claasehmke/Remote-Controller-Accessory-for-Ventilators/Raspberry/include/tcp_messages.hpp

#ifndef REMOTE_CONTROLLER_RASPI_TCP_MESSAGES_HPP
#define REMOTE_CONTROLLER_RASPI_TCP_MESSAGES_HPP

namespace remote_controller_tcp {
// messages
    const uint32_t MSG_ACTUATOR_CONTROL_ID = 0x00;

    struct MSG_ACTUATOR_CONTROL{
        const int32_t message_id = MSG_ACTUATOR_CONTROL_ID;
        int32_t time;
        int32_t rotation_update; //bool
        int32_t rotation; //steps in both directions
        int32_t push_update; //bool
        int32_t push; //bool
    } __attribute__((packed));

}
#endif //REMOTE_CONTROLLER_RASPI_TCP_MESSAGES_HPP
